kartik-rao-0701/Blinkenbytes/images/pcb top layer.jpg

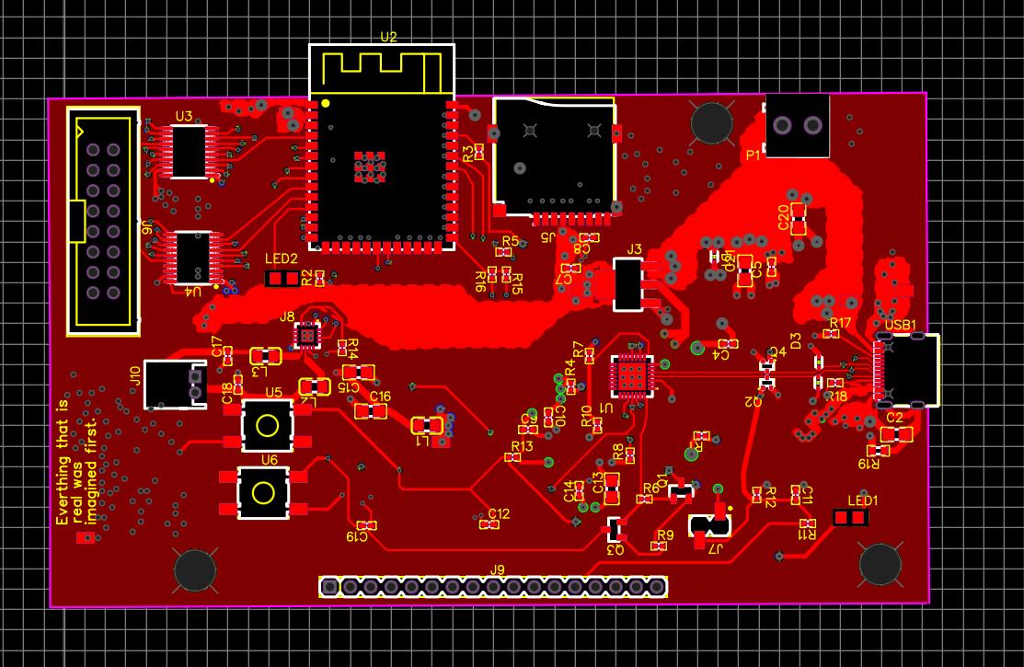
images/pcb top layer.jpg
